tinypico/tinypico-hardware/TinyPICO Nano/TinyPICO Nano Drawing.pdf

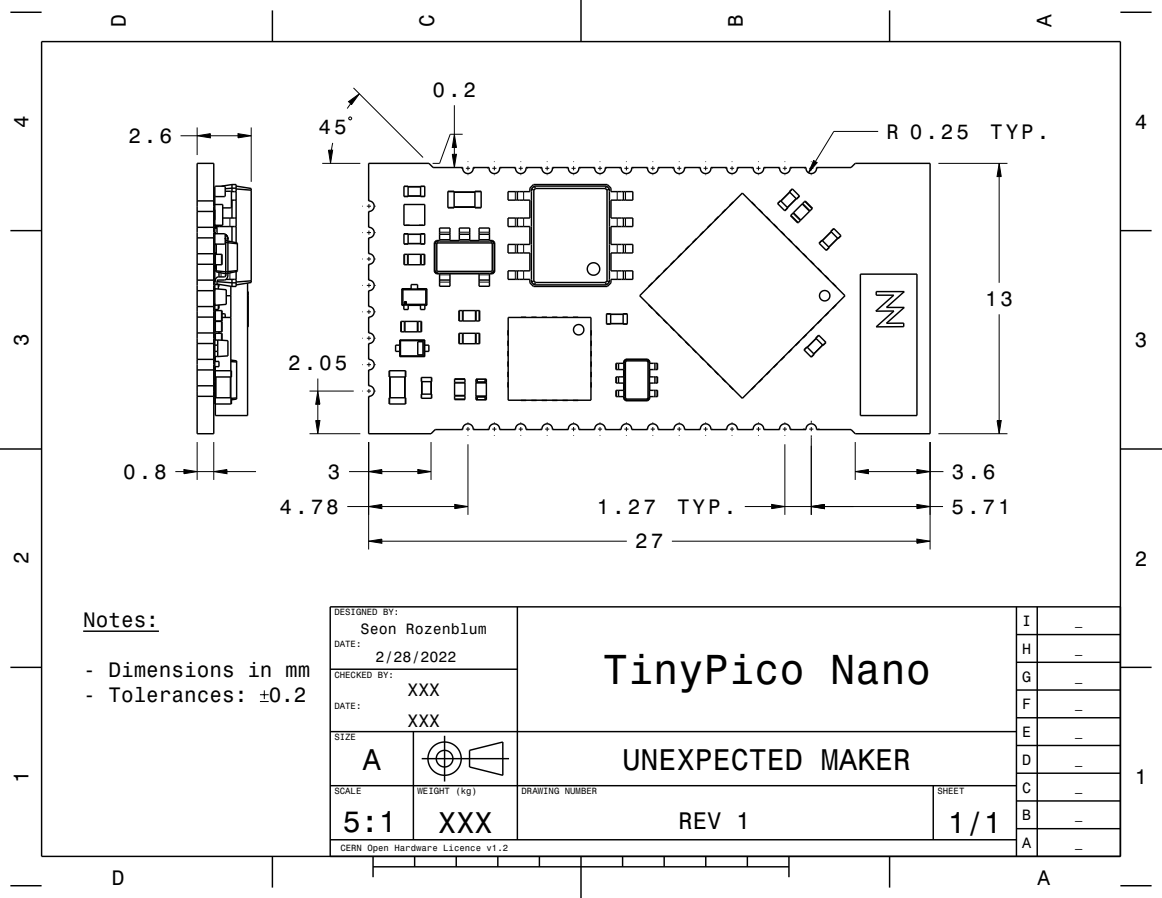
[picture p16: page 1]
CHECKED BY:; - Tolerances:; 1.27 TYP.; R 0.25 TYP.

DESIGNED BY: Seon Rozenblum DATE: 2/28/2022 | TinyPico Nano | I | _

- Dimensions in mm

SIZE A | | | | UNEXPECTED MAKER

SCALE 5:1 | WEIGHT (kg) XXX | DRAWING NUMBER REV 1 | SHEET 1/1

CERN Open Hardware Licence v1.2
